lihzhao14/ESE5160_Highway/images/demo_car.jpg

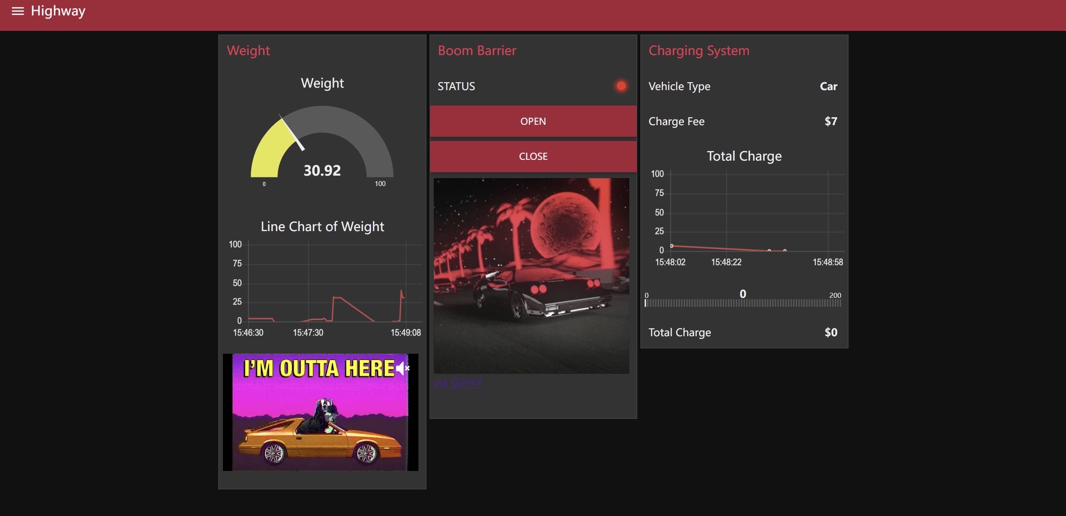
images/demo_car.jpg
