lihzhao14/ESE5160_Highway/pcb/pcb_image/pcb_bottom.png

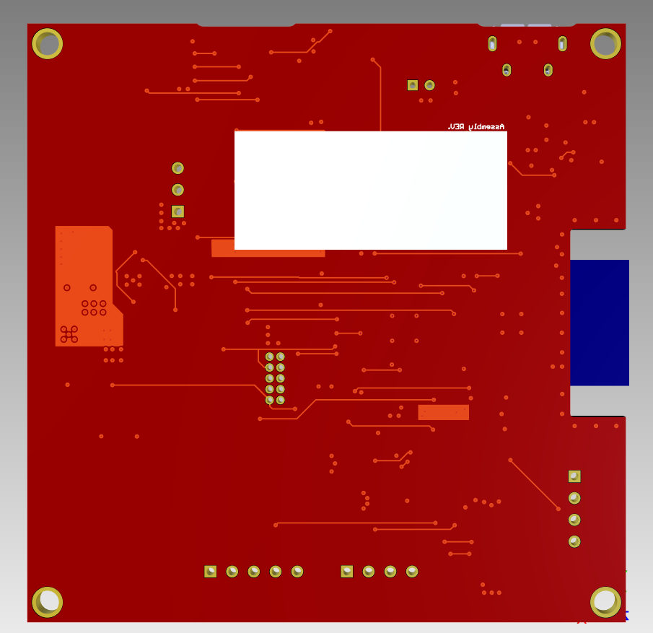
pcb/pcb_image/pcb_bottom.png
