lihzhao14/ESE5160_Highway/pcb/pcb_image/pcb_top.png

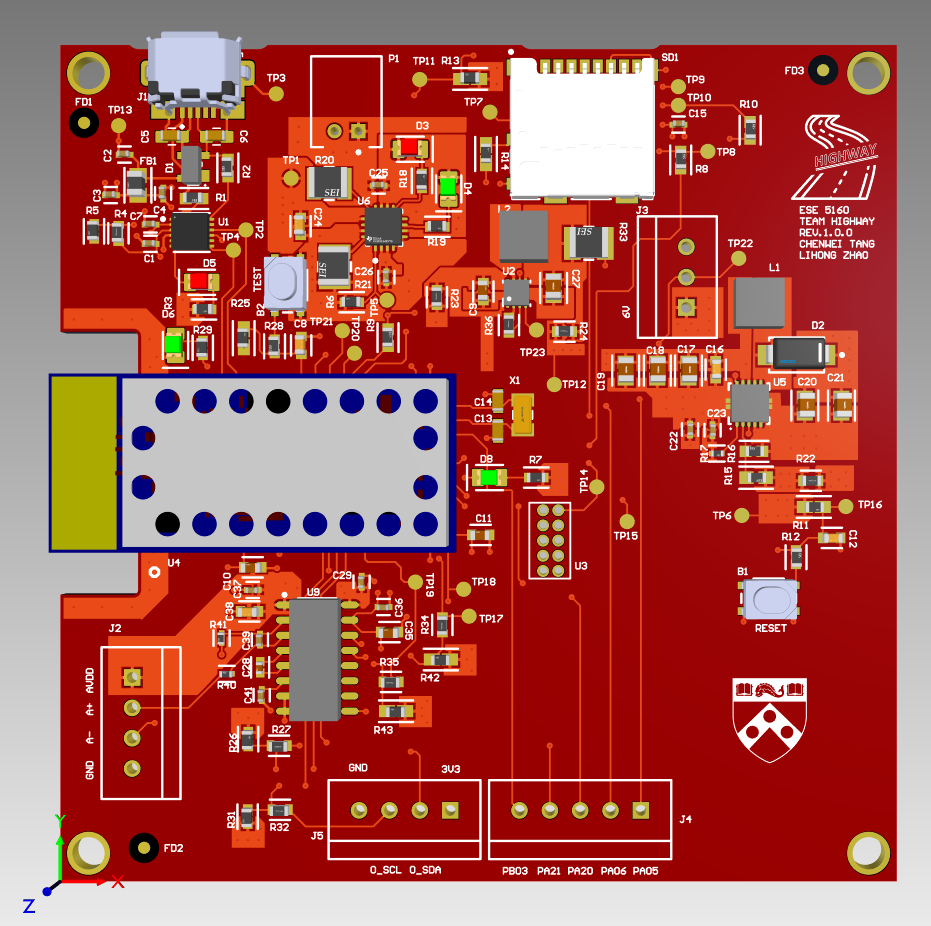
pcb/pcb_image/pcb_top.png
