lihzhao14/ESE5160_Highway/pcb/pcb_image/power_layer.png

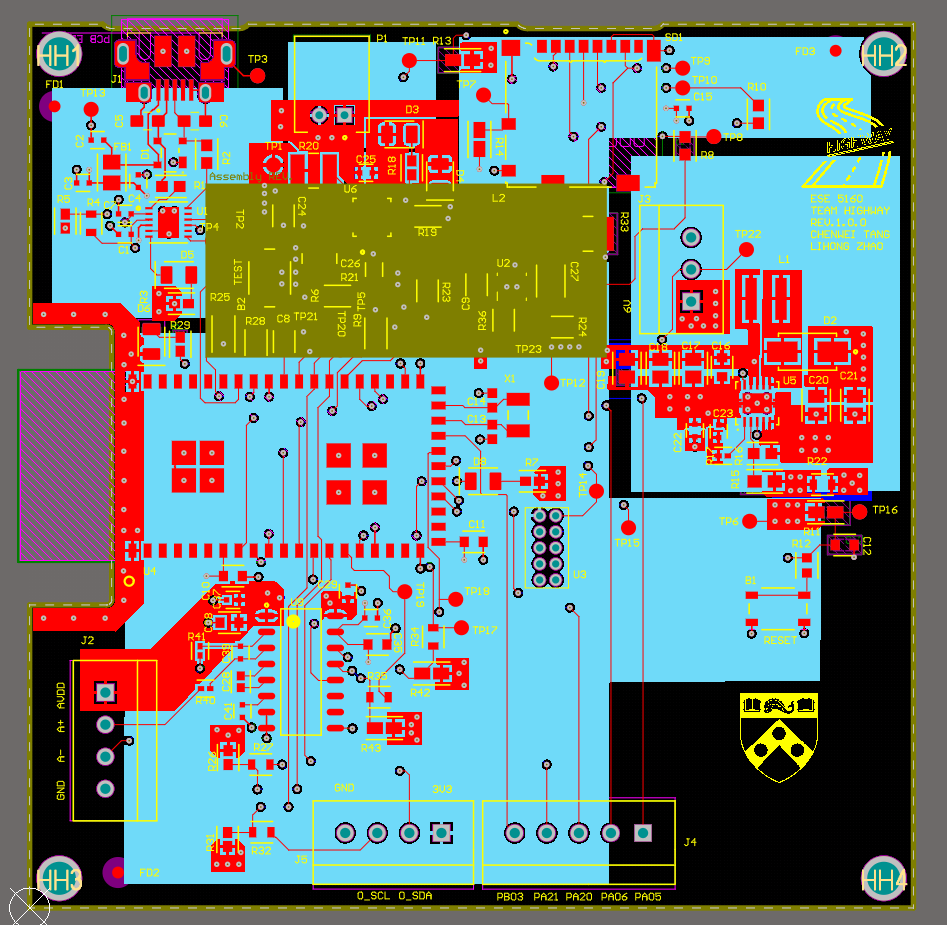
pcb/pcb_image/power_layer.png
