lihzhao14/ESE5160_Highway/code_for_SAWM25/WINC1500_HTTP_DOWNLOADER_EXAMPLE1/src/UiHandlerThread/UiHandlerThread.c

/**
* @file      UiHandlerThread.c
* @brief     File that contains the task code and supporting code for the UI
Thread for ESE516 Spring (Online) Edition
* @author    You! :)
* @date      2020-04-09

******************************************************************************/

/******************************************************************************
 * Includes
 ******************************************************************************/
#include "UiHandlerThread/UiHandlerThread.h"

#include <errno.h>

#include "DistanceDriver/DistanceSensor.h"
#include "IMU/lsm6dso_reg.h"
#include "SeesawDriver/Seesaw.h"
#include "SerialConsole.h"
#include "WifiHandlerThread/WifiHandler.h"
#include "asf.h"
#include "gfx_mono.h"
#include "main.h"
#include "servo/servo.h"
#include "nau7802/nau7802.h"

/******************************************************************************
 * Defines
 ******************************************************************************/

/******************************************************************************
 * Variables
 ******************************************************************************/

/******************************************************************************
 * Forward Declarations
 ******************************************************************************/

/******************************************************************************
 * Callback Functions
 ******************************************************************************/

/******************************************************************************
 * Task Function
 ******************************************************************************/

/**
 * @fn		void vUiHandlerTask( void *pvParameters )
 * @brief	STUDENT TO FILL THIS
 * @details 	student to fill this
 * @param[in]	Parameters passed when task is initialized. In this case we can ignore them!
 * @return		Should not return! This is a task defining function.
 * @note
 */
void vUiHandlerTask(void *pvParameters)
{
    // Do initialization code here
	SerialConsoleWriteString("UI Task Started!");
	configure_tcc();
	servo_setDuty(2);

	
    // Graphics Test - Students to uncomment to test out the OLED driver if you are using it! 
	
    gfx_mono_init();
    gfx_mono_draw_string("ESE516", 0, 8, &sysfont);
    gfx_mono_draw_string("HIGHWAY", 0, 18, &sysfont);
	uint8_t count = 0;
	uint8_t count_nau = 0;
	uint16_t nau_i_total = 0;
	uint16_t nau_f_total = 0;
	char oled_display[24];
	bool servo_flag = false;
	ADCchip_Init();
	

    // Here we start the loop for the UI State Machine
    while (1) {
		ADC_StartConversion();
		struct NauPacket nauvar;
		
		while ((ADC_ReadReg(PU_CTRL_ADDR)&CR_Msk) != CR_DATA_RDY);
		uint32_t ADC_value=ADC_Read_Conversion_Data();
		uint16_t ADC_Array[2];
		//int ADC_Array[2];
		Value_conversion(ADC_value,ADC_Array);
		char help[64];
		//snprintf(help, 64, "input vol = VIN1P - VIN1N = %d\r\n",ADC_Array[0]);
		nauvar.nau_i = ADC_Array[0];
		nauvar.nau_f = ADC_Array[1];
		//nau_i_total = ADC_Array[0] + nau_i_total;
		//nau_f_total = ADC_Array[1] + nau_f_total;
		
		int error = WifiAddNauDataToQueue(&nauvar);
		//if(count_nau!=3)
		//{
			//count_nau = count_nau + 1;
		//}
		//else
		//{
			//count_nau = 0;
			//nauvar.nau_i = nau_i_total/3;
			//nauvar.nau_f = nau_f_total/3;
			//nau_i_total = 0;
			//nau_i_total = 0;
			//int error = WifiAddNauDataToQueue(&nauvar);
		//}
		//
		
		
		if(count!=100)
		{
			count = count + 1;
		}
		else
		{
			count = 0;
			//gfx_mono_init();
			sprintf(oled_display, "%d.%d", ADC_Array[0], ADC_Array[1]);
			gfx_mono_draw_string(oled_display, 0, 8, &sysfont);
		}
		
		
		
        // After execution, you can put a thread to sleep for some time.
        vTaskDelay(50);
    }
}
